Hookander/Shifupi/3D/TestMotorHolderTopv3.stl

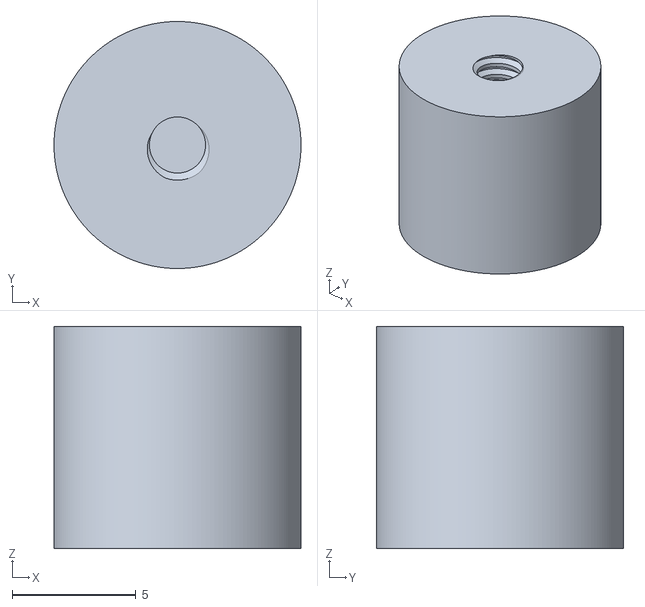
[picture p18: CAD file, 2023-12-07]
3D/TestMotorHolderTopv3.stl
10.00 x 10.00 x 9.00
