Hookander/Shifupi/3D/Pi Holder Top v1.stl

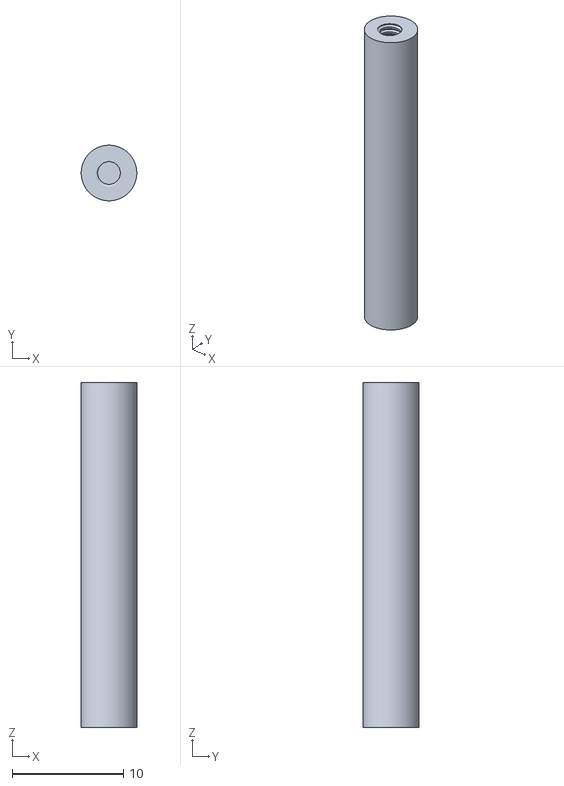
[picture p19: CAD file, 2023-12-07]
3D/Pi Holder Top v1.stl
5.00 x 5.00 x 31.0
