Hookander/Shifupi/3D/test HP holder.stl

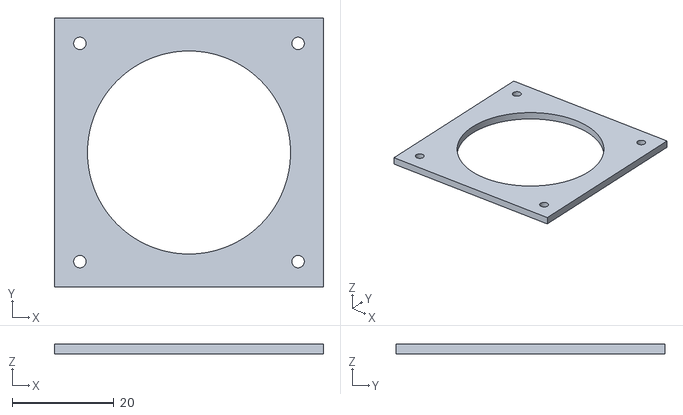
[picture p20: CAD file, 2023-12-07]
3D/test HP holder.stl
53.0 x 53.0 x 2.00
