Hookander/Shifupi/3D/TestMotorHolderv4.stl

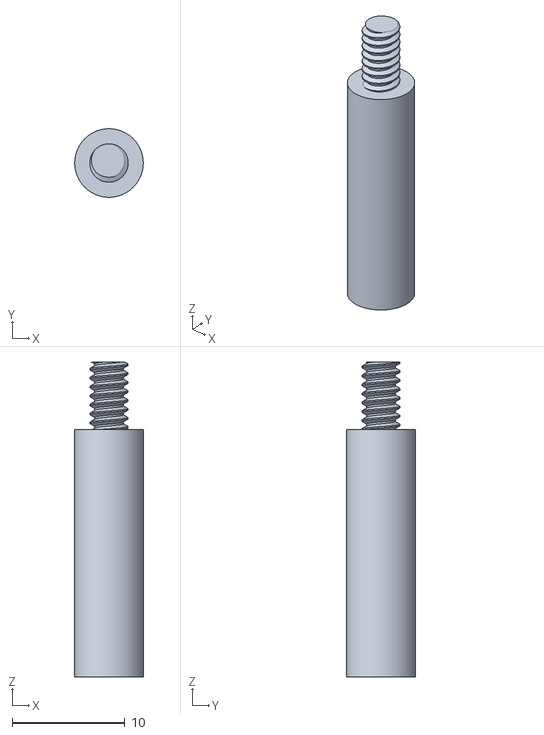
[picture p21: CAD file, 2023-12-07]
3D/TestMotorHolderv4.stl
6.10 x 6.10 x 28.0
