Hookander/Shifupi/3D/Motor Wheel v8.stl

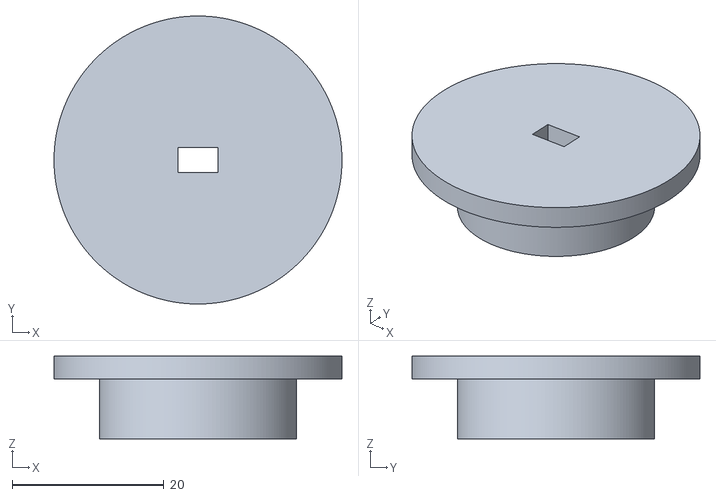
[picture p22: CAD file, 2023-12-07]
3D/Motor Wheel v8.stl
38.0 x 38.0 x 10.9
