Hookander/Shifupi/3D/TestMotorHolderTopv2.stl

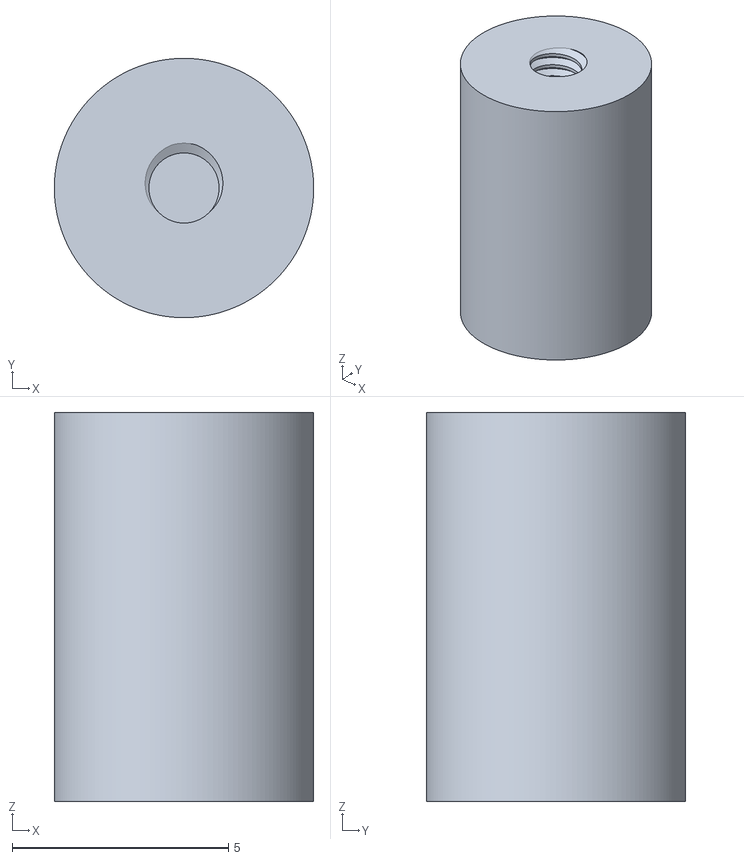
[picture p23: CAD file, 2023-12-07]
3D/TestMotorHolderTopv2.stl
6.00 x 6.00 x 9.00
