Hookander/Shifupi/3D/Test ULN Holder v2.stl

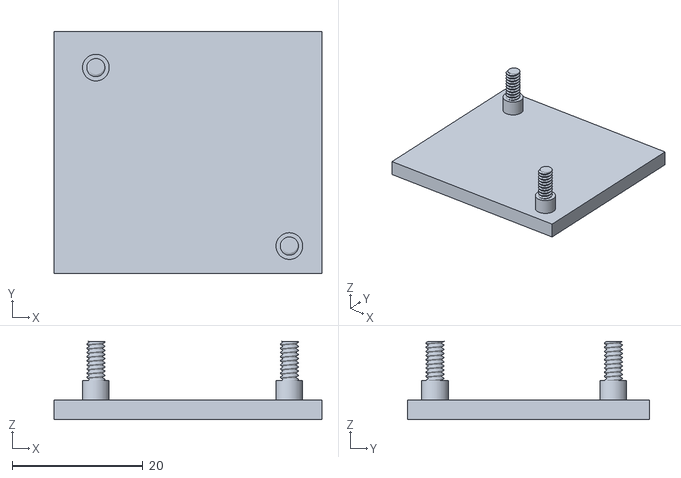
[picture p24: CAD file, 2023-12-07]
3D/Test ULN Holder v2.stl
41.0 x 37.0 x 12.0
