Hookander/Shifupi/3D/Test ULN Holder.stl

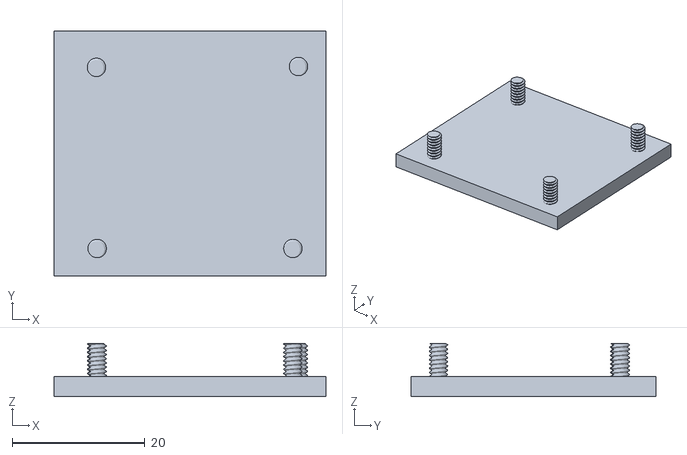
[picture p25: CAD file, 2023-12-07]
3D/Test ULN Holder.stl
41.0 x 37.0 x 8.00
